kzrtn/track-lost/marbastlib/3d/CON_SM06B-SRSS-TB.step

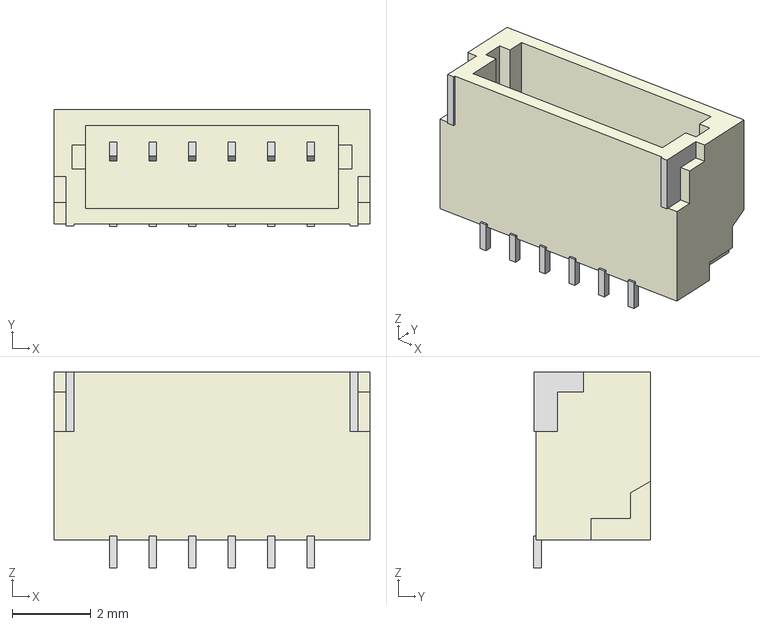
[picture p15: CAD file, 2022-07-03]
marbastlib/3d/CON_SM06B-SRSS-TB.step
8.00 x 2.96 x 4.95 mm
