kzrtn/track-lost/marbastlib/3d/Switch_ESP3020.step

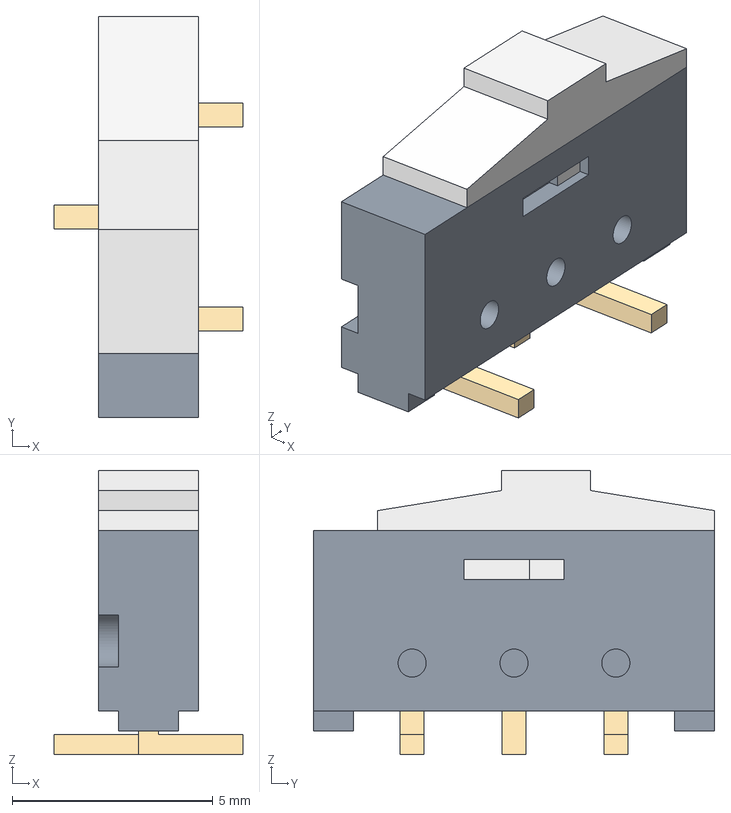
[picture p16: CAD file, 2022-07-03]
marbastlib/3d/Switch_ESP3020.step
4.70 x 10.0 x 7.08 mm
