kzrtn/track-lost/marbastlib/3d/CON_SM05B-SRSS-TB.step

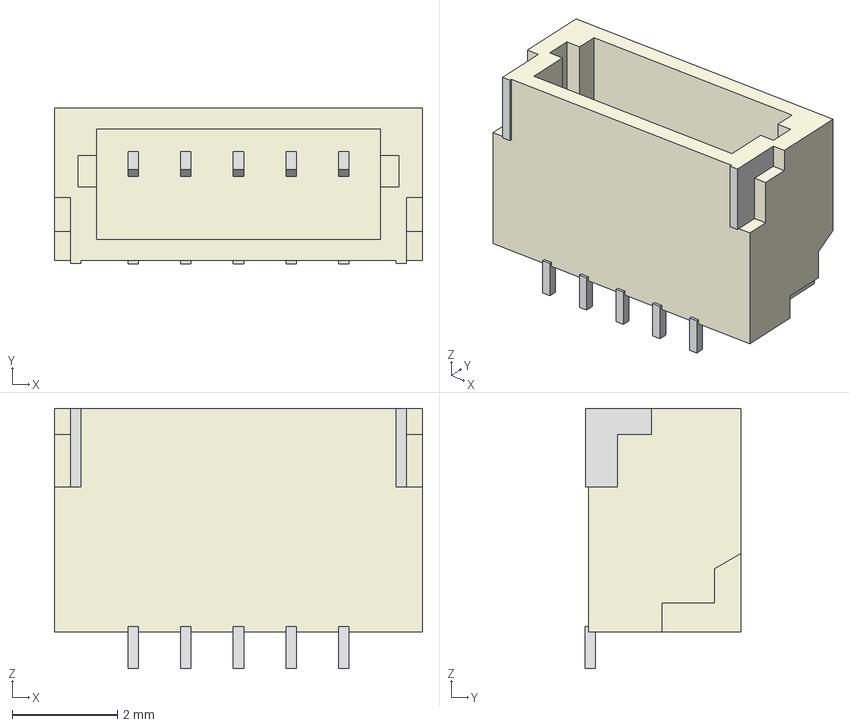
[picture p17: CAD file, 2022-07-03]
marbastlib/3d/CON_SM05B-SRSS-TB.step
7.00 x 2.96 x 4.95 mm
