kzrtn/track-lost/marbastlib/3d/CON_TYPE-C-31-M-12.step

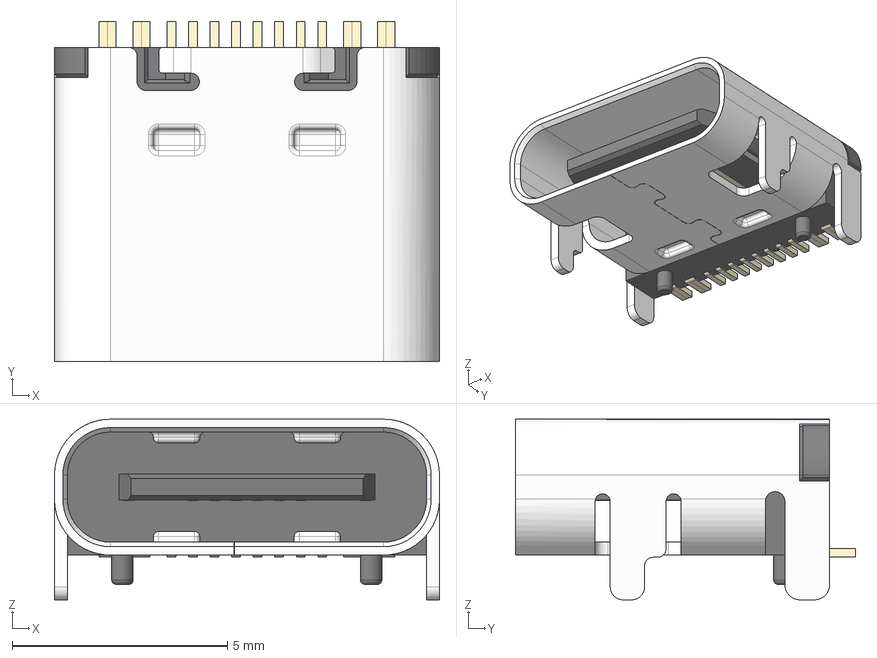
[picture p18: CAD file, 2022-07-03]
marbastlib/3d/CON_TYPE-C-31-M-12.step
8.95 x 7.90 x 4.20 mm
ConPins
PcbPins
Mold
Frame
