kzrtn/track-lost/marbastlib/3d/SW_SSSS213100.step

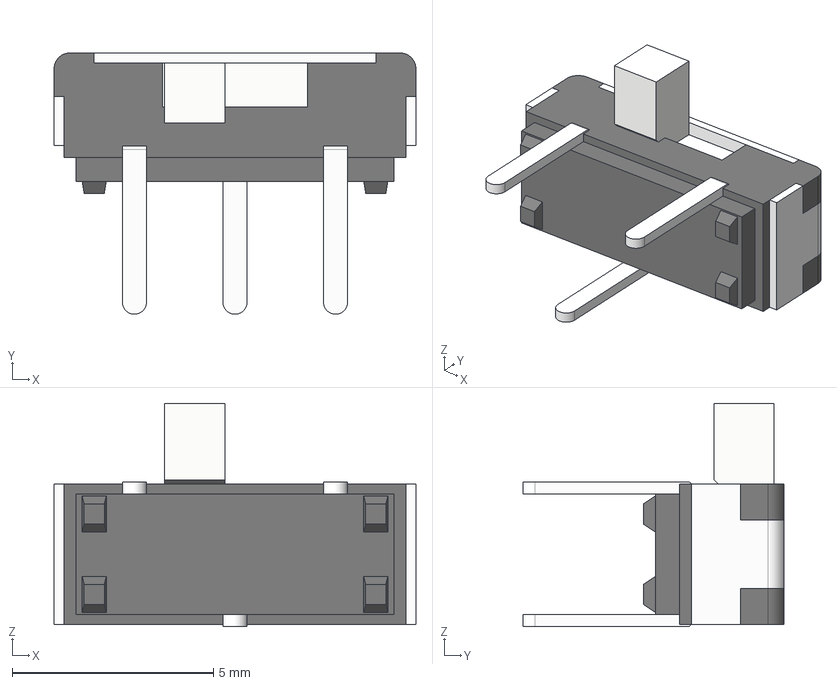
[picture p19: CAD file, 2022-07-03]
marbastlib/3d/SW_SSSS213100.step
9.00 x 6.50 x 5.55 mm
