kzrtn/track-lost/marbastlib/3d/CON_SM13B-SRSS-TB.step

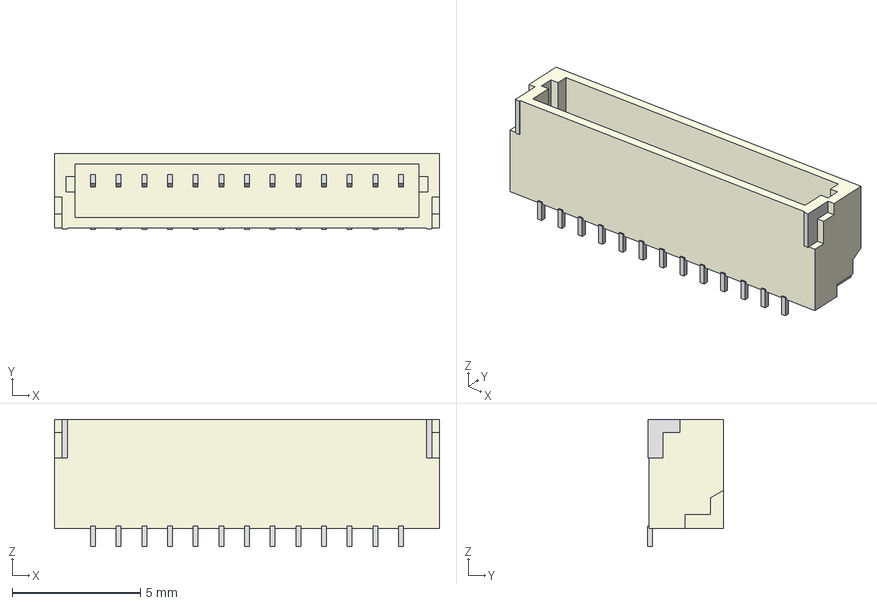
[picture p20: CAD file, 2022-07-03]
marbastlib/3d/CON_SM13B-SRSS-TB.step
15.0 x 2.96 x 4.95 mm
