kzrtn/track-lost/marbastlib/3d/SW_SKHLLC.step

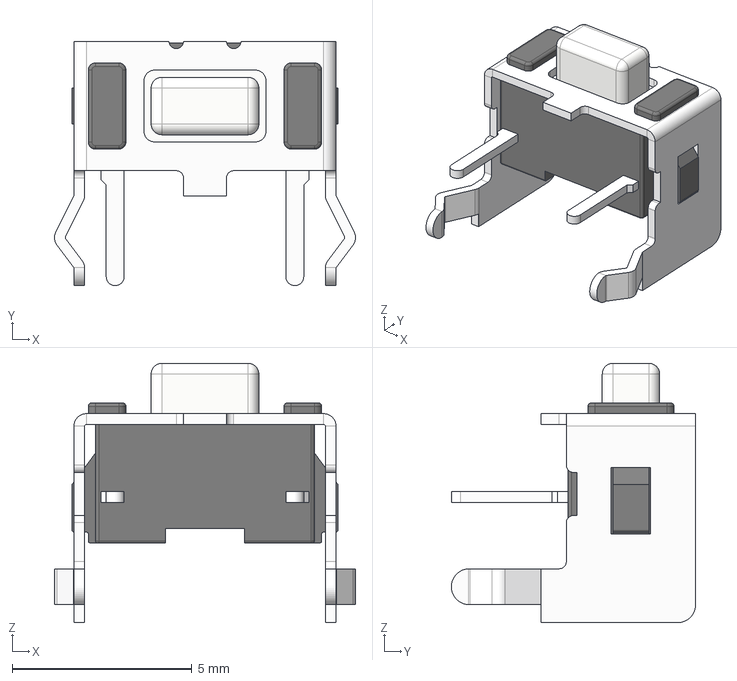
[picture p22: CAD file, 2022-07-03]
marbastlib/3d/SW_SKHLLC.step
8.38 x 6.80 x 7.22 mm
