kzrtn/track-lost/marbastlib/3d/LED_SK6812MINI-E.step

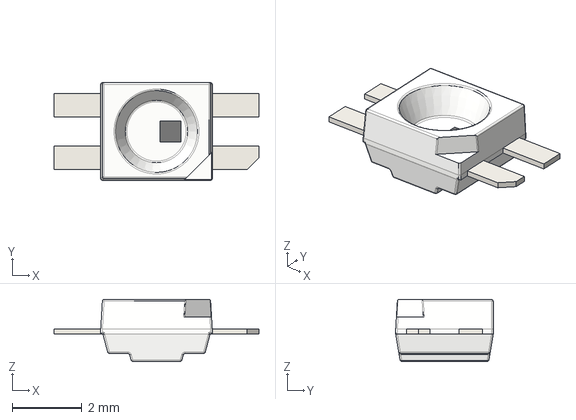
[picture p25: CAD file, 2022-07-03]
marbastlib/3d/LED_SK6812MINI-E.step
5.88 x 2.80 x 1.78 mm
