kzrtn/track-lost/marbastlib/3d/ROT_EC11E.step

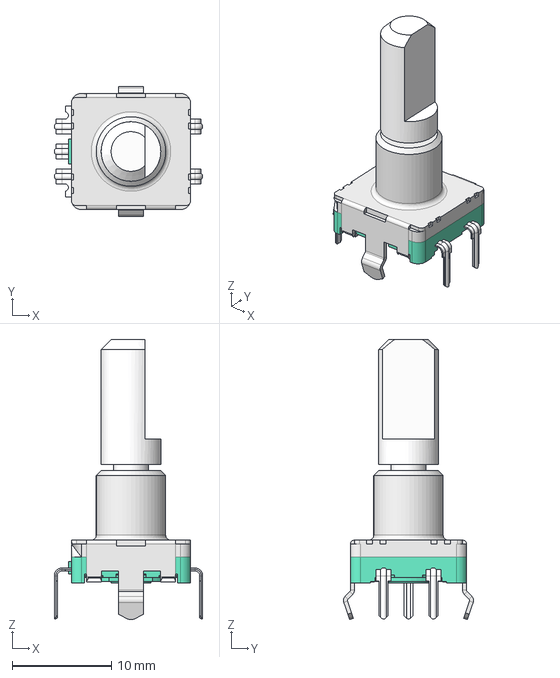
[picture p26: CAD file, 2022-07-03]
marbastlib/3d/ROT_EC11E.step
14.9 x 13.1 x 28.2 mm
