kzrtn/track-lost/LEDs.kicad_sch

## KiCad design LEDs.kicad_sch (2022-07-04)

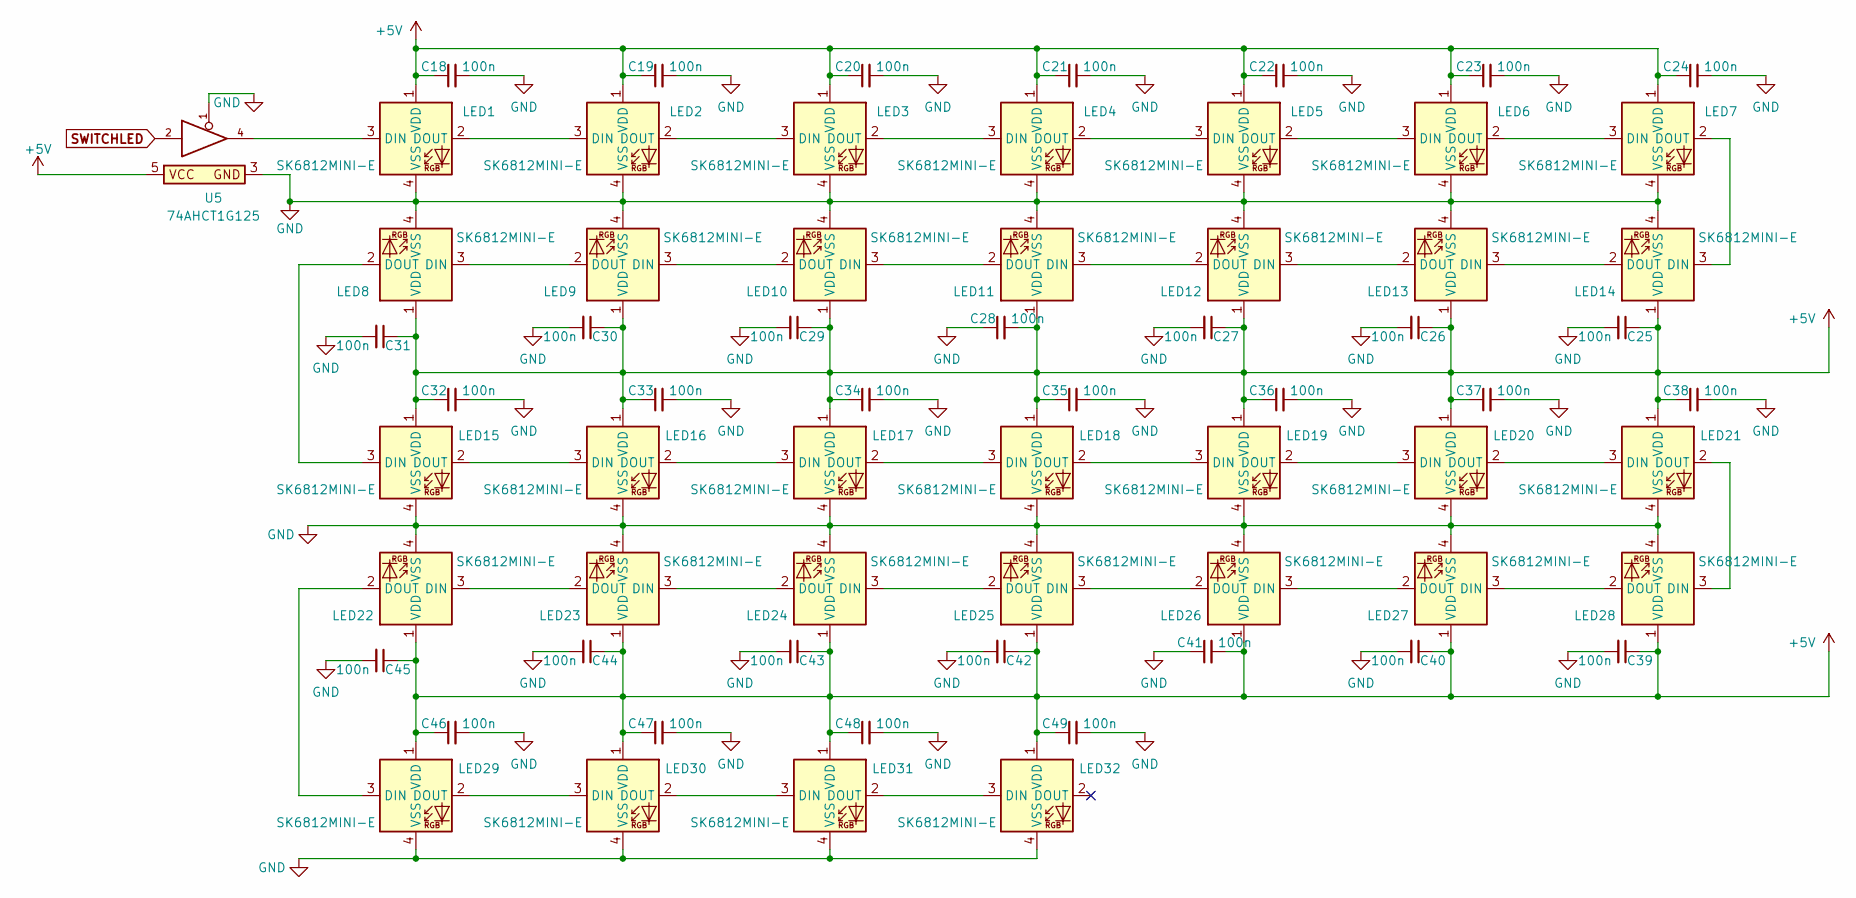
[picture p27: schematic LEDs.kicad_sch]

Parts:
C18, C19, C20, C21, C22, C23, C24, C25, C26, C27, C28, C29, C30, C31, C32, C33, C34, C35, C36, C37, C38, C39, C40, C41, C42, C43, C44, C45, C46, C47, C48, C49: 100n; C_0402_1005Metric
LED1, LED2, LED3, LED4, LED5, LED17, LED18, LED19: SK6812MINI-E; LED_6028R
LED6, LED7, LED8, LED9, LED10, LED11, LED12, LED13, LED14, LED15, LED16, LED20, LED21, LED22, LED23, LED24, LED25, LED26, LED27, LED28, LED29, LED30, LED31, LED32: SK6812MINI-E; LED_WS2812_2020
U5: 74AHCT1G125; SOT-23-5

Connections:
+5V: C18.1, C19.1, C20.1, C21.1, C22.1, C23.1, C24.1, C25.1, C26.1, C27.1, C28.2, C29.1, C30.1, C31.1, C32.1, C33.1, C34.1, C35.1, C36.1, C37.1, C38.1, C39.1, C40.1, C41.2, C42.1, C43.1, C44.1, C45.1, C46.1, C47.1, C48.1, C49.1, LED1.1 (VDD), LED2.1 (VDD), LED3.1 (VDD), LED4.1 (VDD), LED5.1 (VDD), LED6.1 (VDD), LED7.1 (VDD), LED8.1 (VDD), LED9.1 (VDD), LED10.1 (VDD), LED11.1 (VDD), LED12.1 (VDD), LED13.1 (VDD), LED14.1 (VDD), LED15.1 (VDD), LED16.1 (VDD), LED17.1 (VDD), LED18.1 (VDD), LED19.1 (VDD), LED20.1 (VDD), LED21.1 (VDD), LED22.1 (VDD), LED23.1 (VDD), LED24.1 (VDD), LED25.1 (VDD), LED26.1 (VDD), LED27.1 (VDD), LED28.1 (VDD), LED29.1 (VDD), LED30.1 (VDD), LED31.1 (VDD), LED32.1 (VDD), U5.5
GND: C18.2, C19.2, C20.2, C21.2, C22.2, C23.2, C24.2, C25.2, C26.2, C27.2, C28.1, C29.2, C30.2, C31.2, C32.2, C33.2, C34.2, C35.2, C36.2, C37.2, C38.2, C39.2, C40.2, C41.1, C42.2, C43.2, C44.2, C45.2, C46.2, C47.2, C48.2, C49.2, LED1.4 (VSS), LED2.4 (VSS), LED3.4 (VSS), LED4.4 (VSS), LED5.4 (VSS), LED6.4 (VSS), LED7.4 (VSS), LED8.4 (VSS), LED9.4 (VSS), LED10.4 (VSS), LED11.4 (VSS), LED12.4 (VSS), LED13.4 (VSS), LED14.4 (VSS), LED15.4 (VSS), LED16.4 (VSS), LED17.4 (VSS), LED18.4 (VSS), LED19.4 (VSS), LED20.4 (VSS), LED21.4 (VSS), LED22.4 (VSS), LED23.4 (VSS), LED24.4 (VSS), LED25.4 (VSS), LED26.4 (VSS), LED27.4 (VSS), LED28.4 (VSS), LED29.4 (VSS), LED30.4 (VSS), LED31.4 (VSS), LED32.4 (VSS), U5.1, U5.3
unnamed: LED1.2 (DOUT), LED2.3 (DIN)
unnamed: LED1.3 (DIN), U5.4
unnamed: LED2.2 (DOUT), LED3.3 (DIN)
unnamed: LED3.2 (DOUT), LED4.3 (DIN)
unnamed: LED4.2 (DOUT), LED5.3 (DIN)
unnamed: LED5.2 (DOUT), LED6.3 (DIN)
unnamed: LED6.2 (DOUT), LED7.3 (DIN)
unnamed: LED8.3 (DIN), LED9.2 (DOUT)
unnamed: LED9.3 (DIN), LED10.2 (DOUT)
unnamed: LED10.3 (DIN), LED11.2 (DOUT)
unnamed: LED11.3 (DIN), LED12.2 (DOUT)
unnamed: LED12.3 (DIN), LED13.2 (DOUT)
unnamed: LED13.3 (DIN), LED14.2 (DOUT)
unnamed: LED7.2 (DOUT), LED14.3 (DIN)
unnamed: LED15.2 (DOUT), LED16.3 (DIN)
unnamed: LED8.2 (DOUT), LED15.3 (DIN)
unnamed: LED16.2 (DOUT), LED17.3 (DIN)
unnamed: LED17.2 (DOUT), LED18.3 (DIN)
unnamed: LED18.2 (DOUT), LED19.3 (DIN)
unnamed: LED19.2 (DOUT), LED20.3 (DIN)
unnamed: LED20.2 (DOUT), LED21.3 (DIN)
unnamed: LED21.2 (DOUT), LED28.3 (DIN)
unnamed: LED22.2 (DOUT), LED29.3 (DIN)
unnamed: LED22.3 (DIN), LED23.2 (DOUT)
unnamed: LED23.3 (DIN), LED24.2 (DOUT)
unnamed: LED24.3 (DIN), LED25.2 (DOUT)
unnamed: LED25.3 (DIN), LED26.2 (DOUT)
unnamed: LED26.3 (DIN), LED27.2 (DOUT)
unnamed: LED27.3 (DIN), LED28.2 (DOUT)
unnamed: LED29.2 (DOUT), LED30.3 (DIN)
unnamed: LED30.2 (DOUT), LED31.3 (DIN)
unnamed: LED31.2 (DOUT), LED32.3 (DIN)
SWITCHLED: U5.2
