kzrtn/track-lost/track-lost.kicad_sch

## KiCad design track-lost.kicad_sch (2022-07-04)

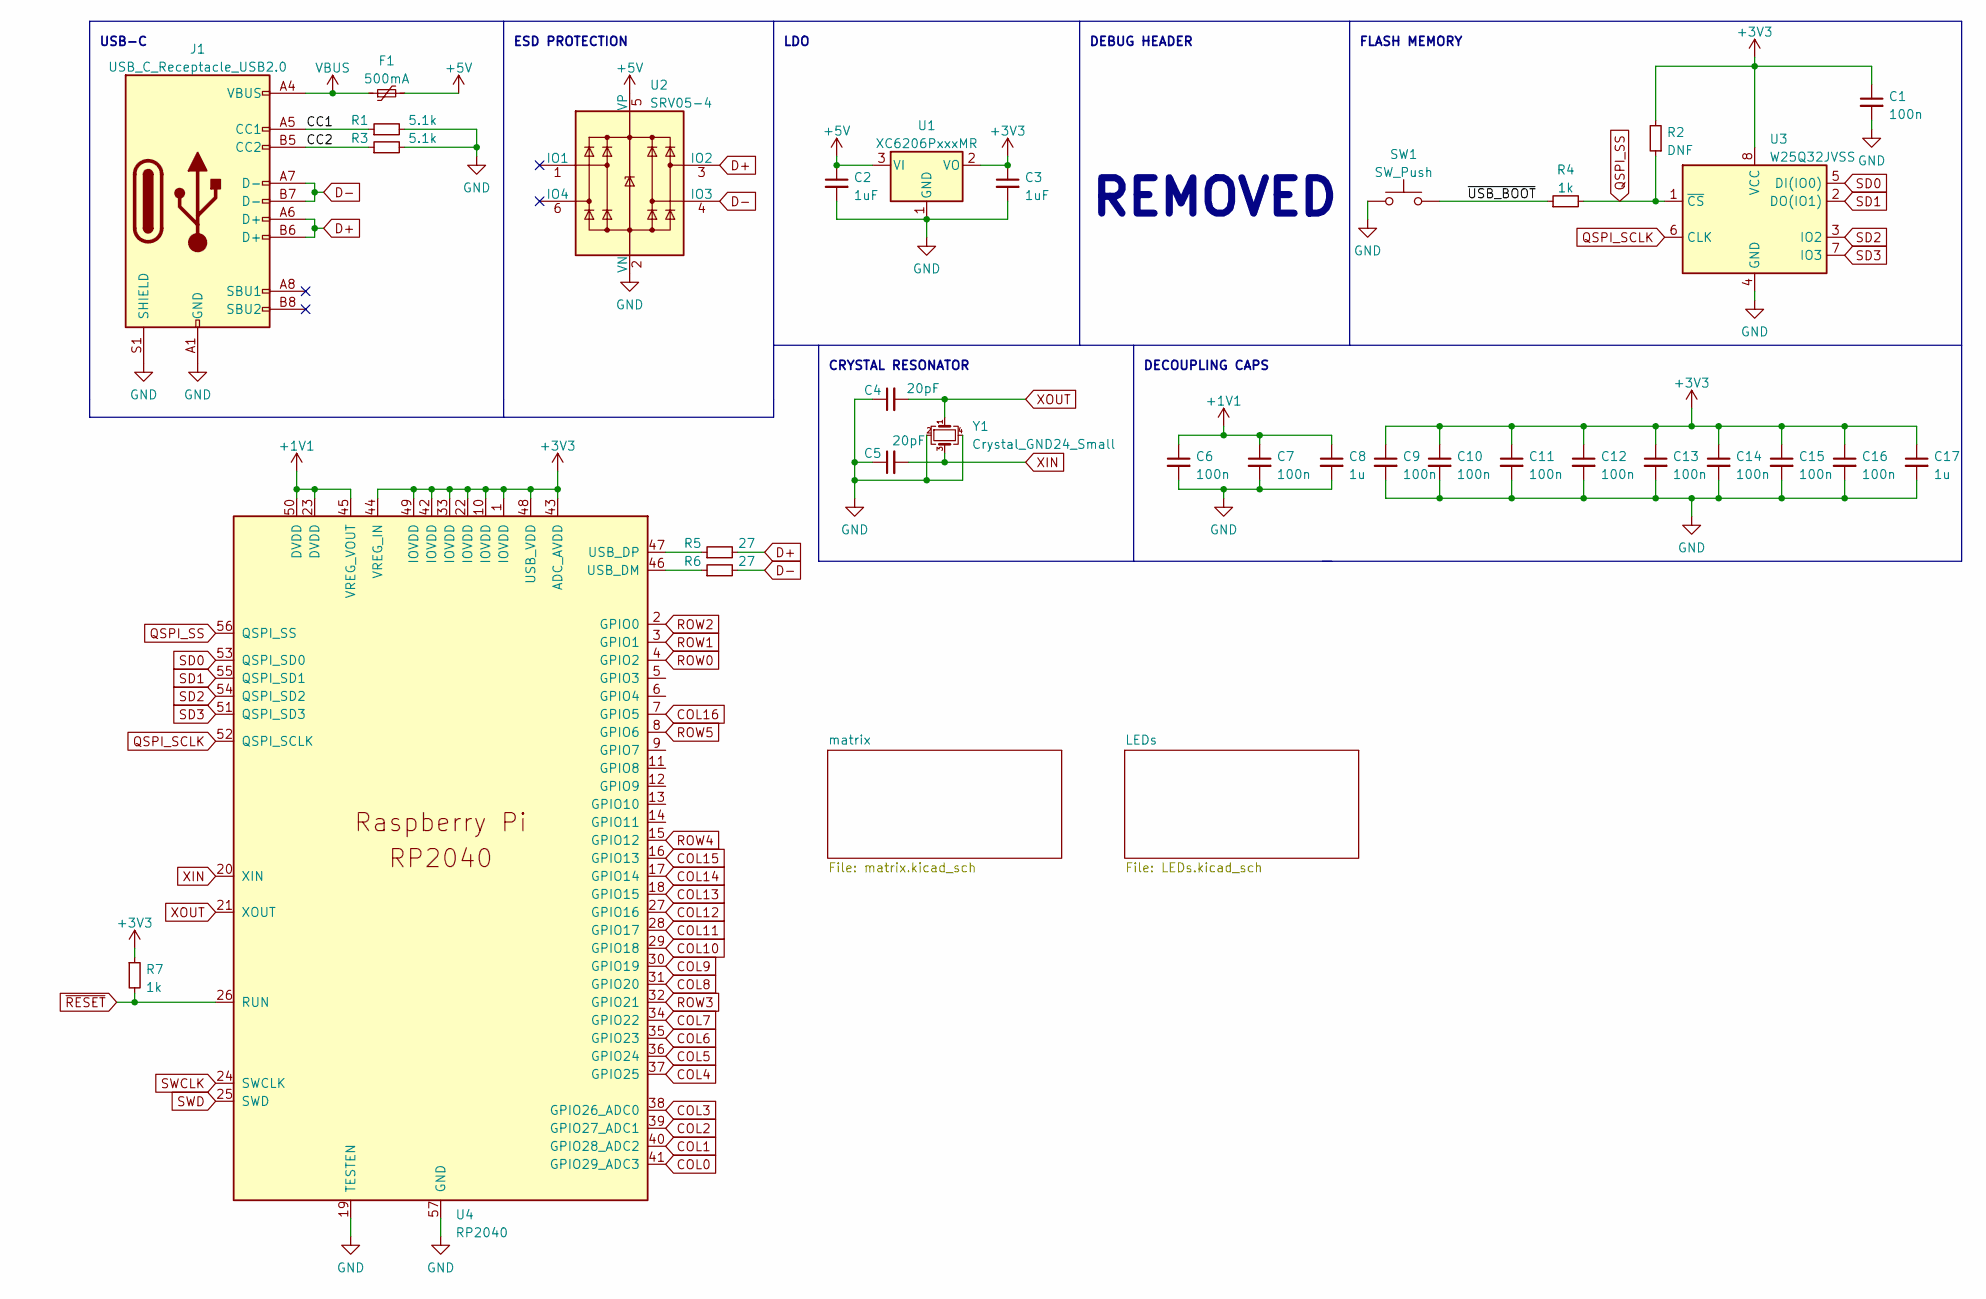
[picture p29: schematic track-lost.kicad_sch]

Parts:
C1, C6, C7, C9, C10, C11, C12, C13, C14, C15, C16: 100n; C_0402_1005Metric
C2, C3: 1uF; C_0402_1005Metric
C4, C5: 20pF; C_0402_1005Metric
C8, C17: 1u; C_0402_1005Metric
F1: 500mA; Fuse_0402_1005Metric
J1: USB_C_Receptacle_USB2.0; USB_C_Receptacle_HRO_TYPE-C-31-M-12
R1, R3: 5.1k; R_0402_1005Metric
R2: DNF; R_0402_1005Metric
R4, R7: 1k; R_0402_1005Metric
R5, R6: 27; R_0402_1005Metric
SW1: SW_Push; SW_SPST_SKQG_WithStem
U1: XC6206PxxxMR; SOT-23
U2: SRV05-4; SOT-23-6-routable
U3: W25Q32JVSS; SOIC-8_5.23x5.23mm_P1.27mm
U4: RP2040; RP2040-QFN-56
Y1: Crystal_GND24_Small; Crystal_SMD_3225-4Pin_3.2x2.5mm

Connections:
+1V1: C6.1, C7.1, C8.1, U4.23 (DVDD), U4.45 (VREG_VOUT), U4.50 (DVDD)
+3V3: C1.1, C3.1, C9.1, C10.1, C11.1, C12.1, C13.1, C14.1, C15.1, C16.1, C17.1, R2.2, R7.1, U1.2 (VO), U3.8 (VCC), U4.1 (IOVDD), U4.10 (IOVDD), U4.22 (IOVDD), U4.33 (IOVDD), U4.42 (IOVDD), U4.43 (ADC_AVDD), U4.44 (VREG_IN), U4.48 (USB_VDD), U4.49 (IOVDD)
+5V: C2.1, F1.2, U1.3 (VI), U2.5 (VP)
CC1: J1.A5 (CC1), R1.1
CC2: J1.B5 (CC2), R3.1
COL0: U4.41 (GPIO29_ADC3)
COL1: U4.40 (GPIO28_ADC2)
COL2: U4.39 (GPIO27_ADC1)
COL3: U4.38 (GPIO26_ADC0)
COL4: U4.37 (GPIO25)
COL5: U4.36 (GPIO24)
COL6: U4.35 (GPIO23)
COL7: U4.34 (GPIO22)
COL8: U4.31 (GPIO20)
COL9: U4.30 (GPIO19)
COL10: U4.29 (GPIO18)
COL11: U4.28 (GPIO17)
COL12: U4.27 (GPIO16)
COL13: U4.18 (GPIO15)
COL14: U4.17 (GPIO14)
COL15: U4.16 (GPIO13)
COL16: U4.7 (GPIO5)
D+: J1.A6 (D+), J1.B6 (D+), R5.2, U2.3 (IO2)
D-: J1.A7 (D-), J1.B7 (D-), R6.2, U2.4 (IO3)
GND: C1.2, C2.2, C3.2, C4.1, C5.1, C6.2, C7.2, C8.2, C9.2, C10.2, C11.2, C12.2, C13.2, C14.2, C15.2, C16.2, C17.2, J1.A1 (GND), J1.A12 (GND), J1.B1 (GND), J1.B12 (GND), J1.S1 (SHIELD), R1.2, R3.2, SW1.1, U1.1 (GND), U2.2 (VN), U3.4 (GND), U4.19 (TESTEN), U4.57 (GND), Y1.2, Y1.4
unnamed: R5.1, U4.47 (USB_DP)
unnamed: R6.1, U4.46 (USB_DM)
QSPI_SCLK: U3.6 (CLK), U4.52 (QSPI_SCLK)
QSPI_SS: R2.1, R4.2, U3.1 (~CS), U4.56 (QSPI_SS)
ROW0: U4.4 (GPIO2)
ROW1: U4.3 (GPIO1)
ROW2: U4.2 (GPIO0)
ROW3: U4.32 (GPIO21)
ROW4: U4.15 (GPIO12)
ROW5: U4.8 (GPIO6)
SD0: U3.5 (DI(IO0)), U4.53 (QSPI_SD0)
SD1: U3.2 (DO(IO1)), U4.55 (QSPI_SD1)
SD2: U3.3 (IO2), U4.54 (QSPI_SD2)
SD3: U3.7 (IO3), U4.51 (QSPI_SD3)
SWCLK: U4.24 (SWCLK)
SWD: U4.25 (SWD)
VBUS: F1.1, J1.A4 (VBUS), J1.A9 (VBUS), J1.B4 (VBUS), J1.B9 (VBUS)
XIN: C5.2, U4.20 (XIN), Y1.3
XOUT: C4.2, U4.21 (XOUT), Y1.1
~RESET: R7.2, U4.26 (RUN)
~USB_BOOT: R4.1, SW1.2

Notes on the sheet:
REMOVED
DEBUG HEADER
USB-C
FLASH MEMORY
ESD PROTECTION
CRYSTAL RESONATOR
DECOUPLING CAPS
LDO
